PricelessToolkit/SOILSENS-V5W/img/sens-kc.jpg

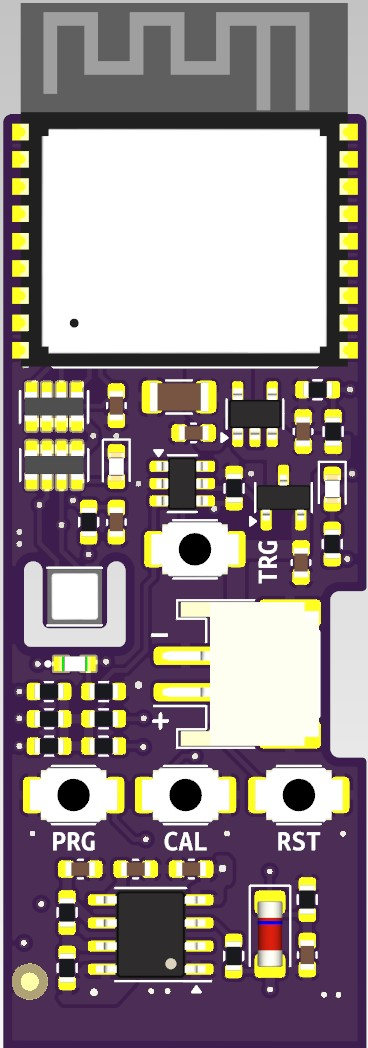
img/sens-kc.jpg
